michaelmcdaniel/postal-clock/pins.h

#pragma once

#include <Arduino.h>

namespace Pins {
constexpr uint8_t kOledSda = 0;
constexpr uint8_t kOledScl = 1;
constexpr uint8_t kRtcSda = 6;
constexpr uint8_t kRtcScl = 7;
constexpr uint8_t kLightAdc = 26;
constexpr uint8_t kInfoButton = 8;
}  // namespace Pins
